IRNAS/bGeigieIntegrated/testing/wifi_test/wifi_test.ino

/*
   Copyright (c) 2016 RedBear

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
   The above copyright notice and this permission notice shall be included in all copies or substantial portions of the Software.

   THE SOFTWARE IS PROVIDED "AS IS", WITHOUT WARRANTY OF ANY KIND, EXPRESS OR IMPLIED, INCLUDING BUT NOT LIMITED TO THE WARRANTIES OF MERCHANTABILITY,
   FITNESS FOR A PARTICULAR PURPOSE AND NONINFRINGEMENT. IN NO EVENT SHALL THE AUTHORS OR COPYRIGHT HOLDERS BE LIABLE FOR ANY CLAIM, DAMAGES OR OTHER
   LIABILITY, WHETHER IN AN ACTION OF CONTRACT, TORT OR OTHERWISE, ARISING FROM, OUT OF OR IN CONNECTION WITH THE SOFTWARE OR THE USE OR OTHER DEALINGS
   IN THE SOFTWARE.
*/

/*
    This is a simple TCP server, telnet to this sketch with an IP assigned for Duo.
    e.g. telnet 192.168.0.5 8888
*/

#if defined(ARDUINO)
SYSTEM_MODE(MANUAL);//do not connect to cloud
#else
SYSTEM_MODE(AUTOMATIC);//connect to cloud
#endif

/* Modify the bellowing definitions for your AP/Router.*/
#define SSID     "open.wlan-si.net"
#define PASSWROD ""

#define MAX_CLIENT_NUM   3

TCPServer server = TCPServer(8888);
TCPClient client[MAX_CLIENT_NUM];

void setup() {
  char addr[16];

  Serial.begin(115200);
  delay(5000);

  WiFi.on();
  WiFi.setCredentials(SSID, PASSWROD, WPA2);
  WiFi.connect();

  Serial.println("Waiting for an IP address...\n");
  while (!WiFi.ready()) {
    delay(1000);
  }

  // Wait IP address to be updated.
  IPAddress localIP = WiFi.localIP();
  while (localIP[0] == 0) {
    localIP = WiFi.localIP();
    delay(1000);
  }

  sprintf(addr, "%u.%u.%u.%u", localIP[0], localIP[1], localIP[2], localIP[3]);
  Serial.println(addr);

  server.begin();
}

void loop() {
  for (uint8_t i = 0; i < MAX_CLIENT_NUM; i++) {
    if (client[i].connected()) {
      Serial.println("Connected by TCP client.");
      client[i].println("Hello!");
    }
    else {
      client[i] = server.available();
    }
  }

  delay(2000);
}
