IRNAS/bGeigieIntegrated/testing/cnt_led_IRover/cnt_led_IRover.ino

#if defined(ARDUINO) 
SYSTEM_MODE(MANUAL);//do not connect to cloud
#else
SYSTEM_MODE(AUTOMATIC);//connect to cloud
#endif

int led1 = D0;
int led2 = A2;

void setup() {
  pinMode(led1, OUTPUT);
  pinMode(led2, OUTPUT);
}

void loop() {
  digitalWrite(led1, HIGH);
  digitalWrite(led2, HIGH);

  delay(1000);

  digitalWrite(led1, LOW);
  digitalWrite(led2, LOW);

  delay(1000);
}
